GeiserX/PiSpot-Show/docs/photos/blue-case-buttons-sd-slot.jpg

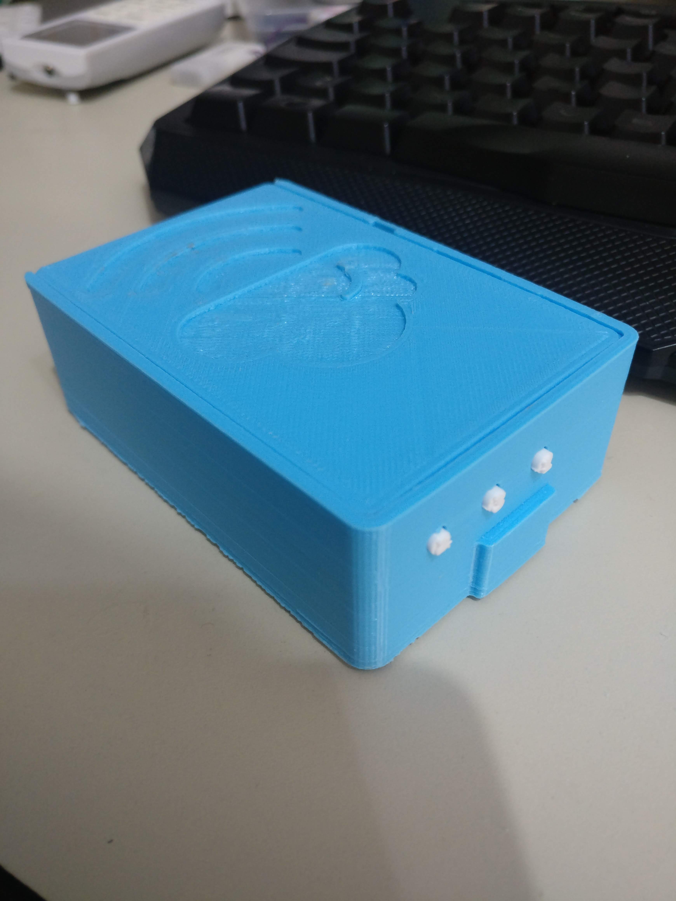
docs/photos/blue-case-buttons-sd-slot.jpg
