GeiserX/PiSpot-Show/docs/photos/blue-case-ethernet-view.jpg

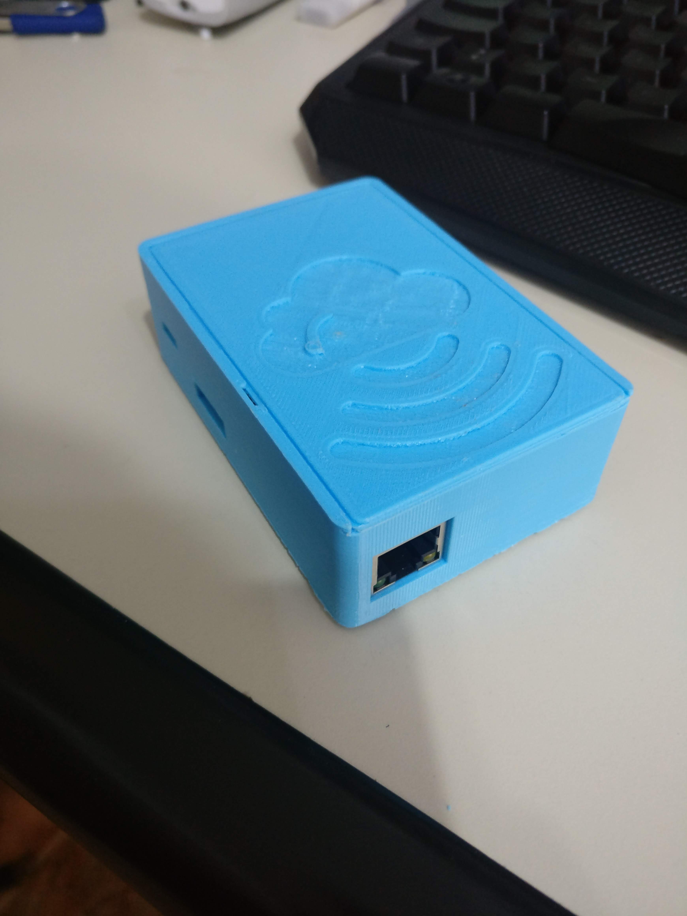
docs/photos/blue-case-ethernet-view.jpg
