GeiserX/PiSpot-Show/docs/photos/pi3-dark-case-ports.jpg

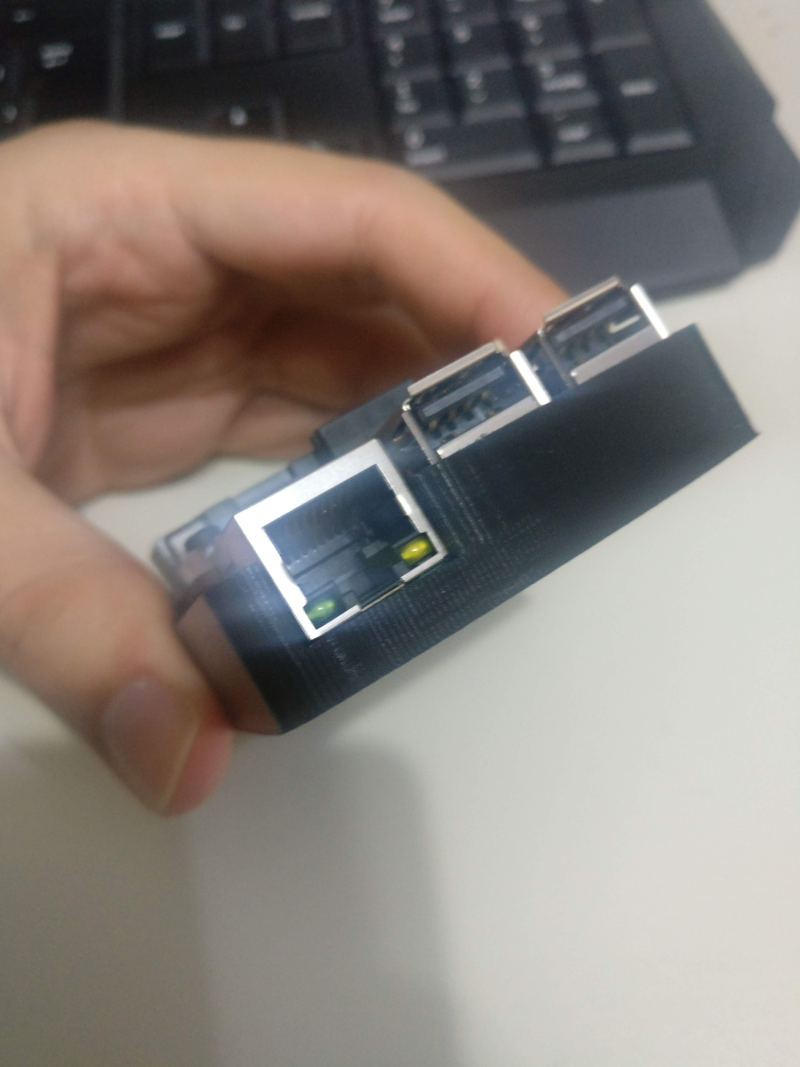
docs/photos/pi3-dark-case-ports.jpg
