GeiserX/PiSpot-Show/docs/photos/pijuice-battery-closeup.jpg

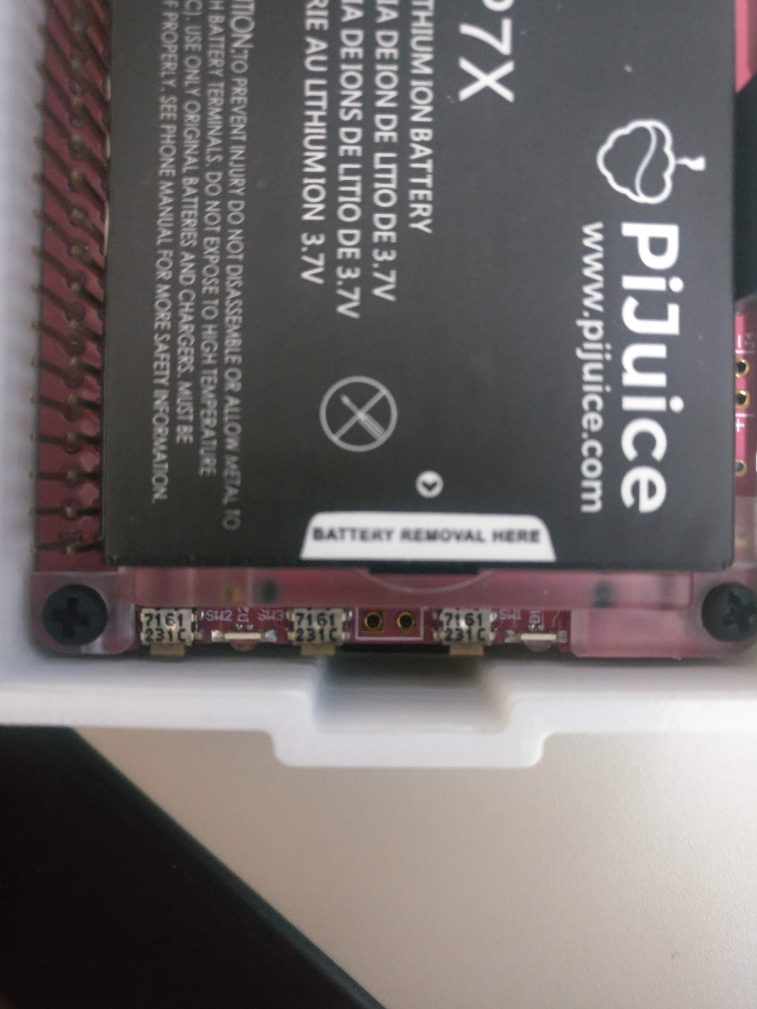
docs/photos/pijuice-battery-closeup.jpg
