GeiserX/PiSpot-Show/docs/photos/pijuice-in-case-hand.jpg

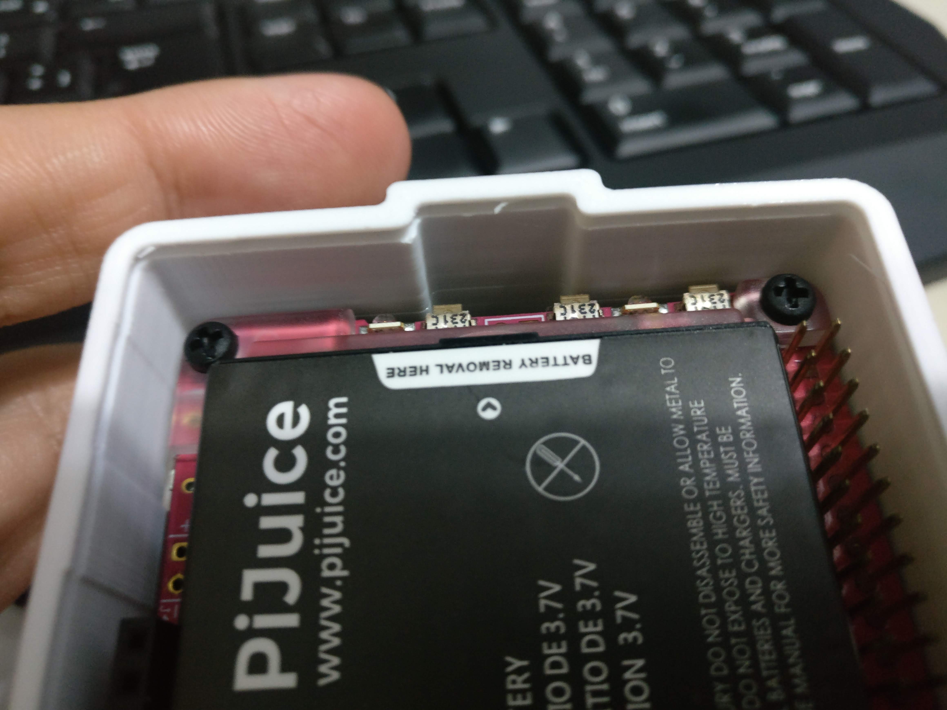
docs/photos/pijuice-in-case-hand.jpg
