GeiserX/PiSpot-Show/docs/photos/prototype-ups-hat-tft-front.jpg

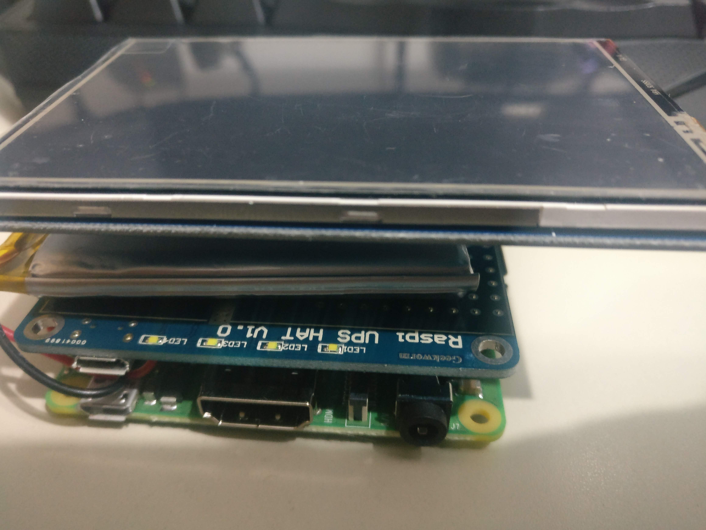
docs/photos/prototype-ups-hat-tft-front.jpg
