GeiserX/PiSpot-Show/docs/photos/white-case-bottom-rubber-feet.jpg

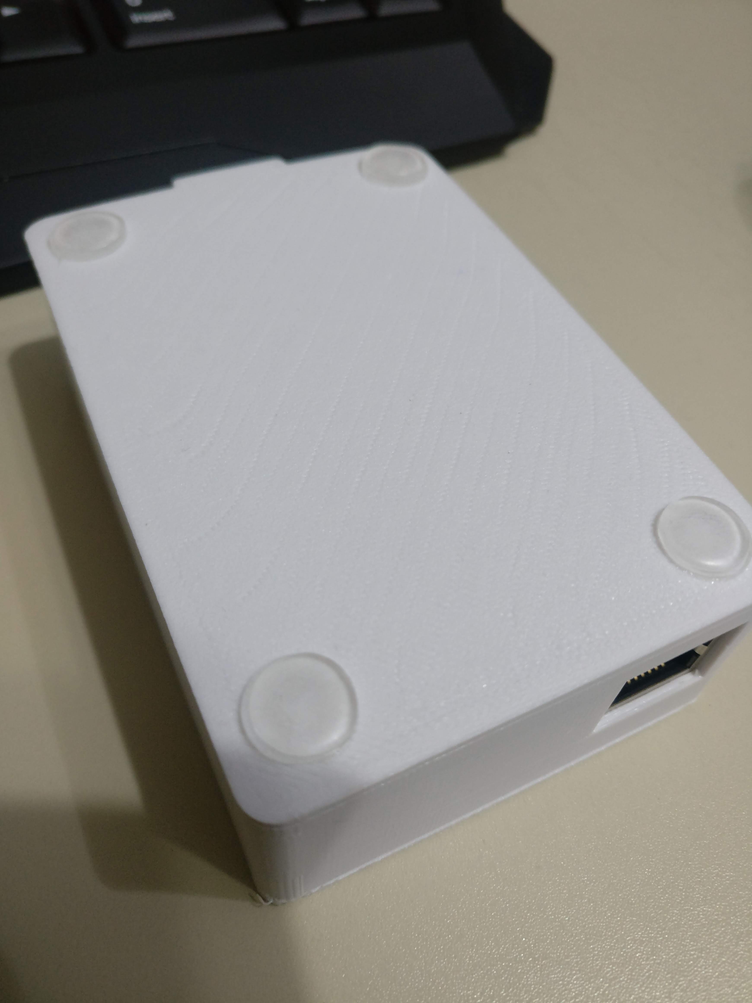
docs/photos/white-case-bottom-rubber-feet.jpg
