GeiserX/PiSpot-Show/docs/photos/white-case-top-view.jpg

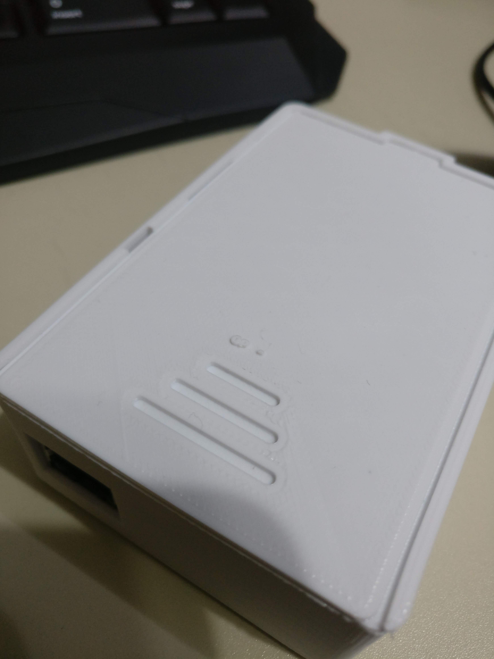
docs/photos/white-case-top-view.jpg
