GeiserX/PiSpot-Show/images/GPConnect_blanc.png

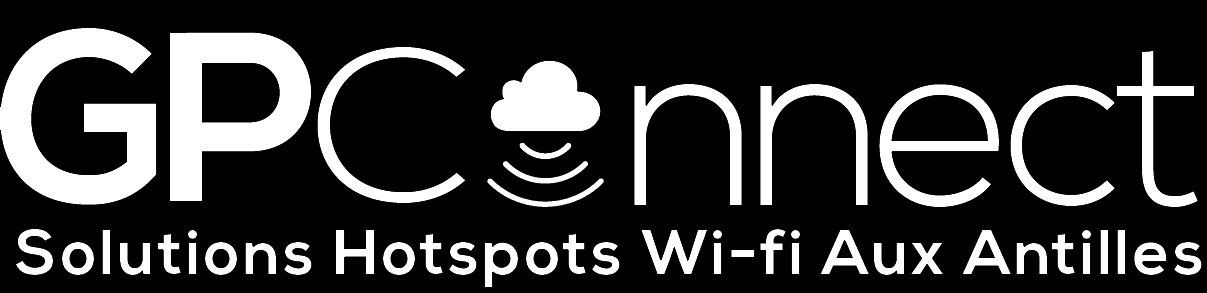
images/GPConnect_blanc.png
